OpenVentilator/OpenVentilator/hardware/Knob-4.sldprt

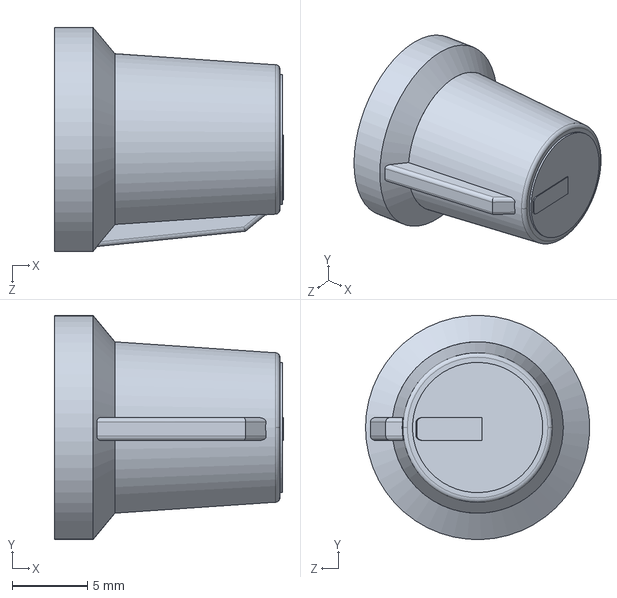
[picture p17: CAD file, 2020-04-01]
hardware/Knob-4.sldprt
15.2 x 14.9 x 14.9 mm
