OpenVentilator/OpenVentilator/hardware/PLEXI_DXF/lower_plate.DXF

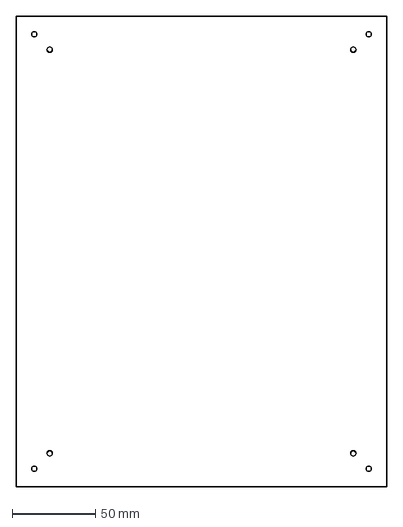
[picture p18: CAD file, 2020-03-31]
hardware/PLEXI_DXF/lower_plate.DXF
222.0 x 282.0 mm
