OpenVentilator/OpenVentilator/hardware/lower_gearbox_plate.SLDPRT

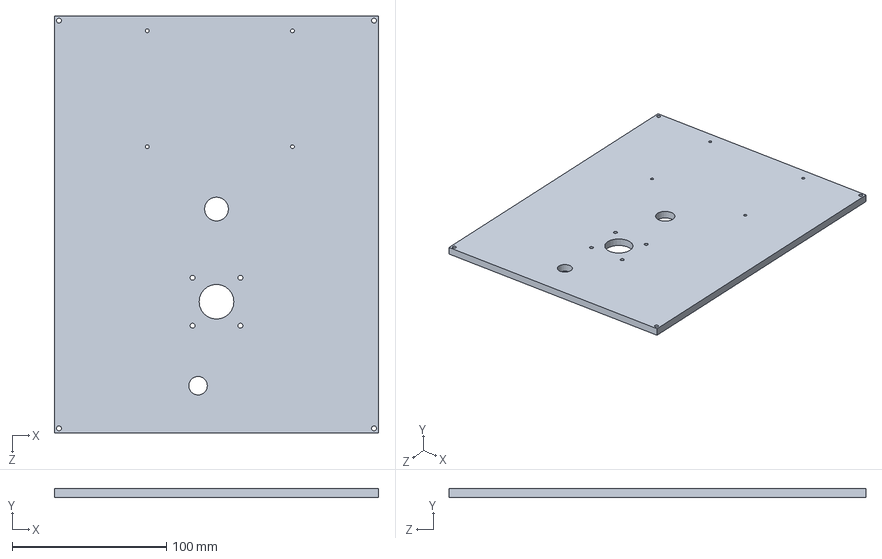
[picture p19: CAD file, 2020-04-01]
hardware/lower_gearbox_plate.SLDPRT
210.0 x 6.00 x 270.0 mm
