OpenVentilator/OpenVentilator/hardware/PLEXI_DXF/side_cover.DXF

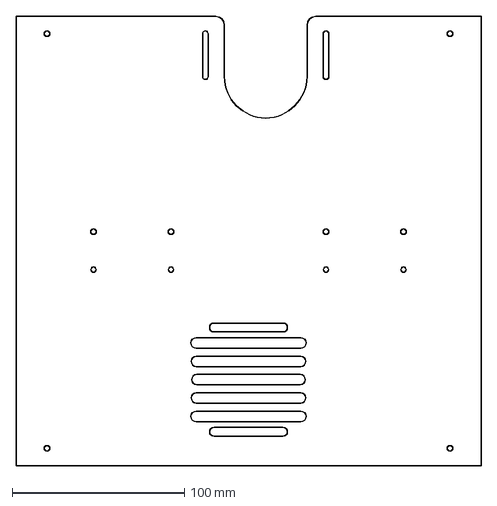
[picture p20: CAD file, 2020-03-31]
hardware/PLEXI_DXF/side_cover.DXF
270.0 x 260.8 mm
