OpenVentilator/OpenVentilator/hardware/lower_plate.SLDPRT

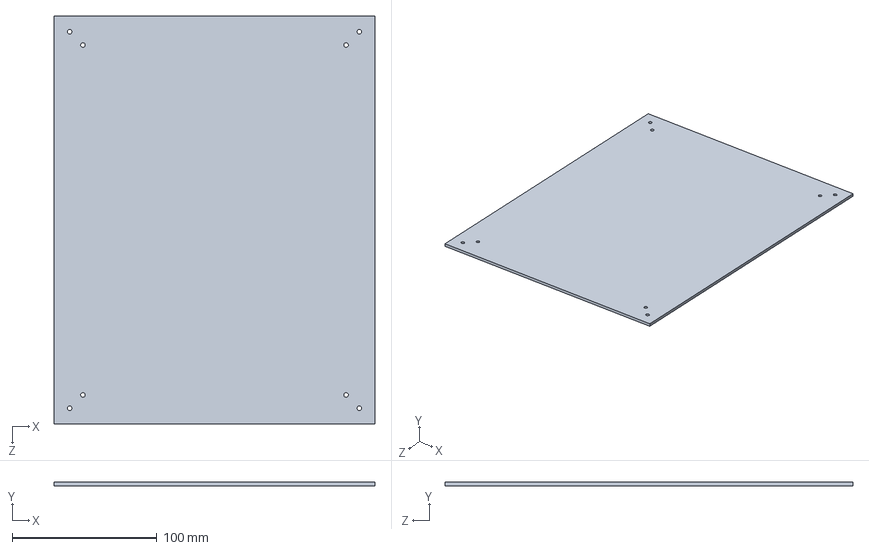
[picture p21: CAD file, 2020-03-31]
hardware/lower_plate.SLDPRT
222.0 x 2.50 x 282.0 mm
