OpenVentilator/OpenVentilator/hardware/PLEXI_DXF/spacershort.DXF

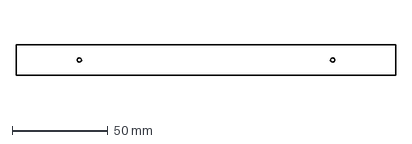
[picture p22: CAD file, 2020-03-31]
hardware/PLEXI_DXF/spacershort.DXF
198.0 x 16.0 mm
