OpenVentilator/OpenVentilator/hardware/PLEXI_DXF/motor_holder.DXF

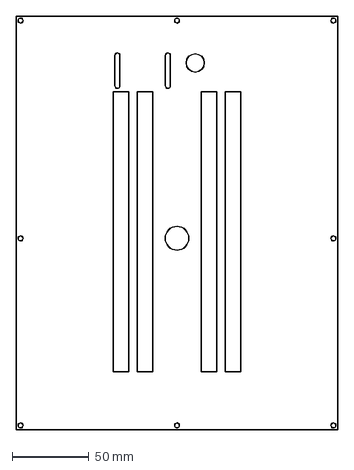
[picture p23: CAD file, 2020-03-31]
hardware/PLEXI_DXF/motor_holder.DXF
210.0 x 270.0 mm
