OpenVentilator/OpenVentilator/hardware/holder_zabalota.SLDPRT

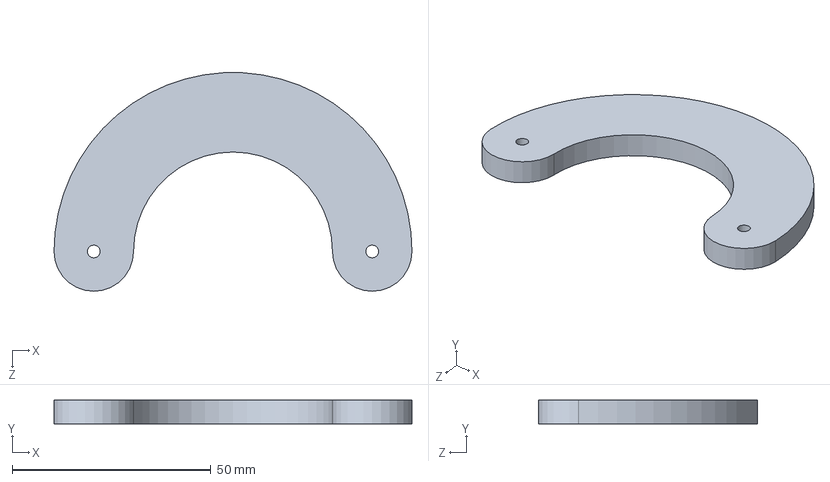
[picture p24: CAD file, 2020-03-31]
hardware/holder_zabalota.SLDPRT
90.0 x 6.00 x 54.9 mm
