OpenVentilator/OpenVentilator/hardware/PLEXI_DXF/side_cover_2.DXF

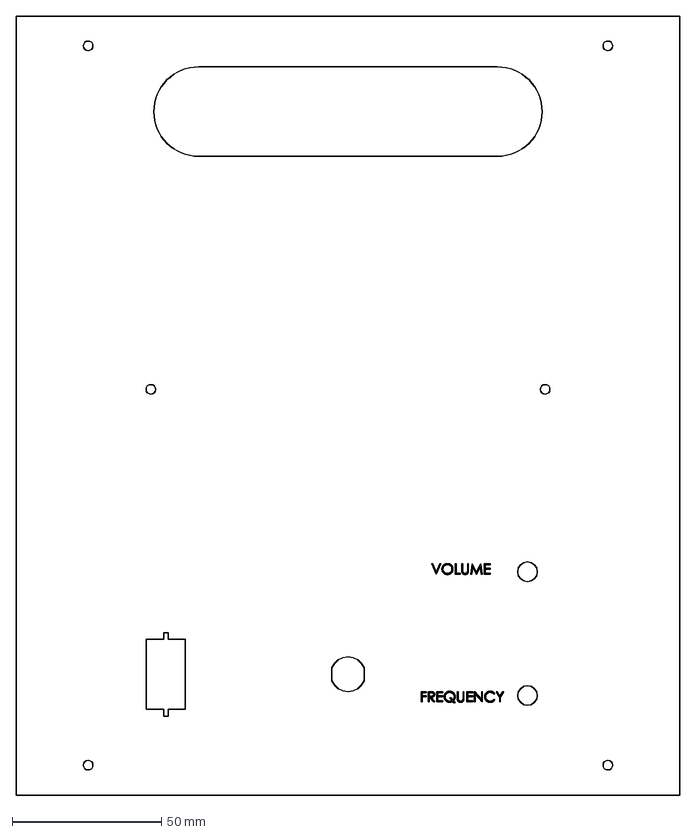
[picture p25: CAD file, 2020-03-31]
hardware/PLEXI_DXF/side_cover_2.DXF
222.0 x 260.8 mm
