OpenVentilator/OpenVentilator/hardware/ambu_adaptor_part2.SLDPRT

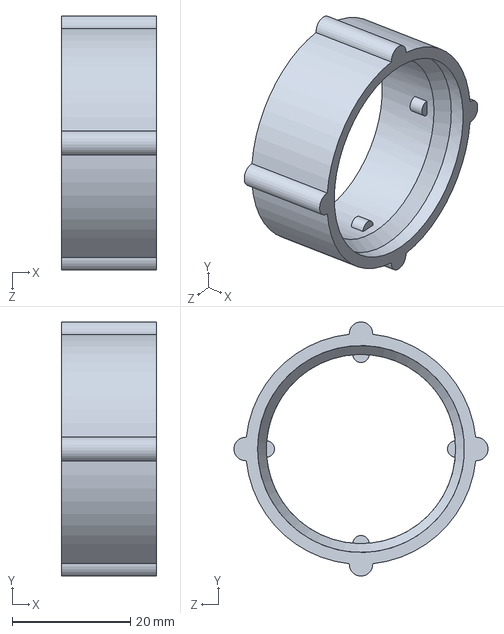
[picture p26: CAD file, 2020-03-31]
hardware/ambu_adaptor_part2.SLDPRT
16.0 x 43.0 x 43.0 mm
