OpenVentilator/OpenVentilator/hardware/PLEXI_DXF/spacerlong.DXF

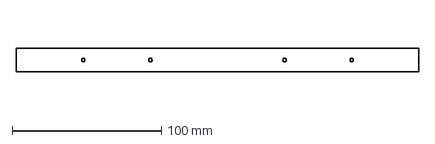
[picture p27: CAD file, 2020-03-31]
hardware/PLEXI_DXF/spacerlong.DXF
270.0 x 16.0 mm
