OpenVentilator/OpenVentilator/hardware/PLEXI_DXF/roulement_guides.DXF

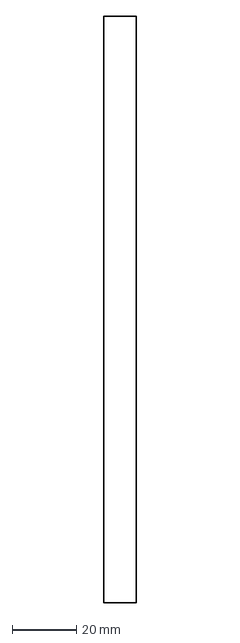
[picture p28: CAD file, 2020-03-31]
hardware/PLEXI_DXF/roulement_guides.DXF
10.0 x 182.6 mm
