OpenVentilator/OpenVentilator/hardware/spacershort.SLDPRT

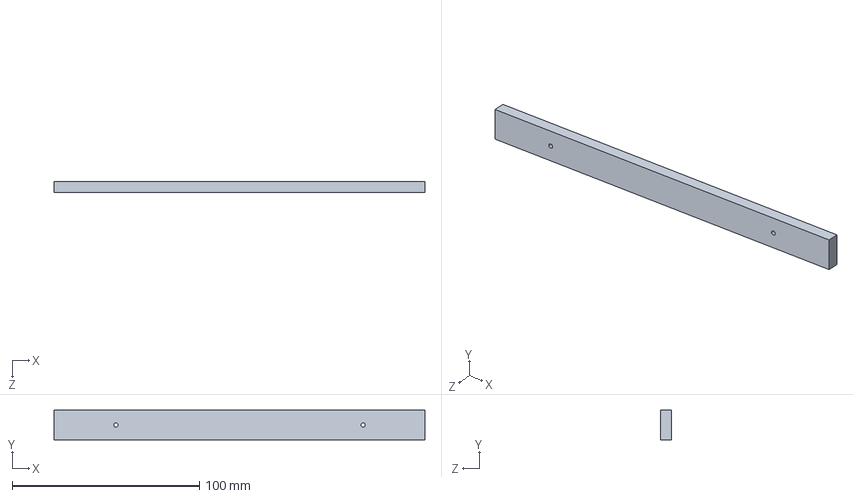
[picture p29: CAD file, 2020-03-31]
hardware/spacershort.SLDPRT
198.0 x 16.0 x 6.00 mm
