OpenVentilator/OpenVentilator/hardware/PLEXI_DXF/side_cover_big.DXF

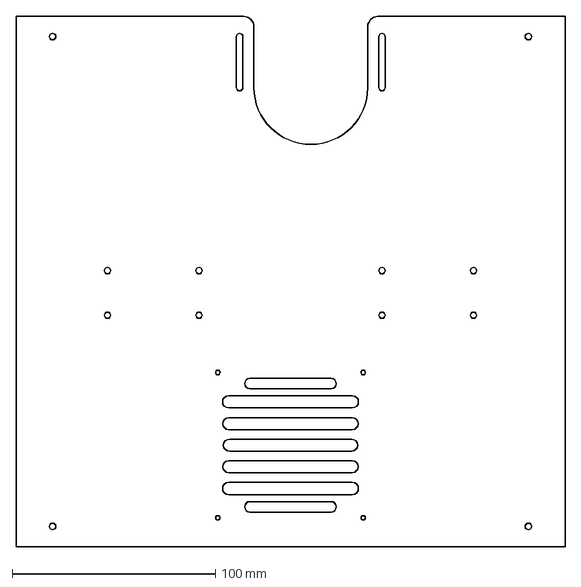
[picture p30: CAD file, 2020-03-31]
hardware/PLEXI_DXF/side_cover_big.DXF
270.0 x 260.8 mm
