OpenVentilator/OpenVentilator/hardware/PLEXI_DXF/top_chassis_plate.DXF

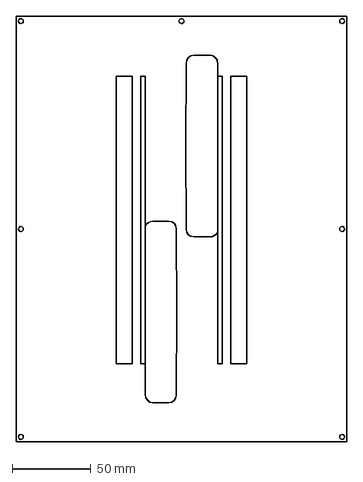
[picture p31: CAD file, 2020-03-31]
hardware/PLEXI_DXF/top_chassis_plate.DXF
210.0 x 270.0 mm
