OpenVentilator/OpenVentilator/hardware/side_cover.SLDPRT

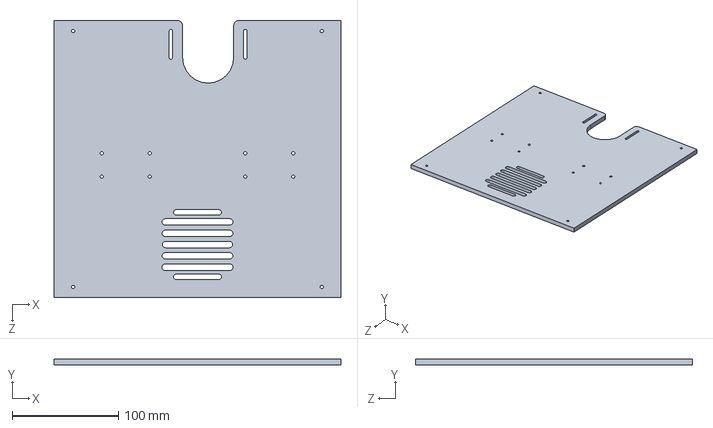
[picture p32: CAD file, 2020-03-31]
hardware/side_cover.SLDPRT
270.0 x 6.00 x 260.8 mm
