OpenVentilator/OpenVentilator/hardware/nema_17_47_gearbox_13.SLDPRT

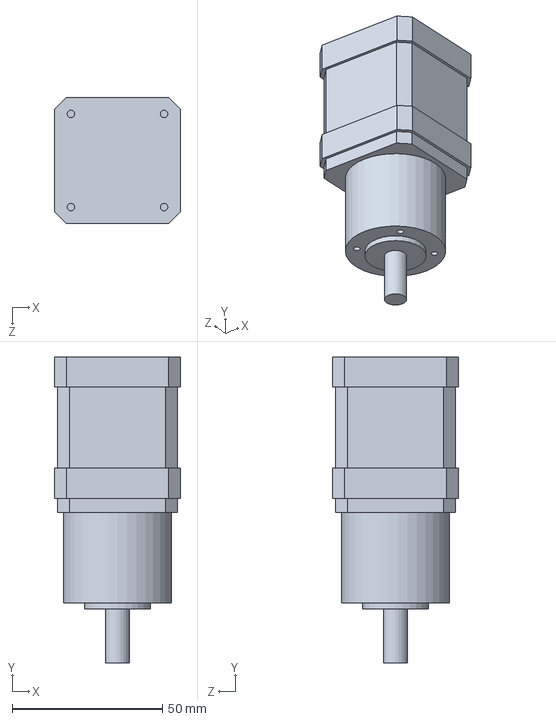
[picture p33: CAD file, 2020-03-31]
hardware/nema_17_47_gearbox_13.SLDPRT
42.0 x 101.8 x 42.0 mm
