OpenVentilator/OpenVentilator/hardware/AMBU_BAG.SLDPRT

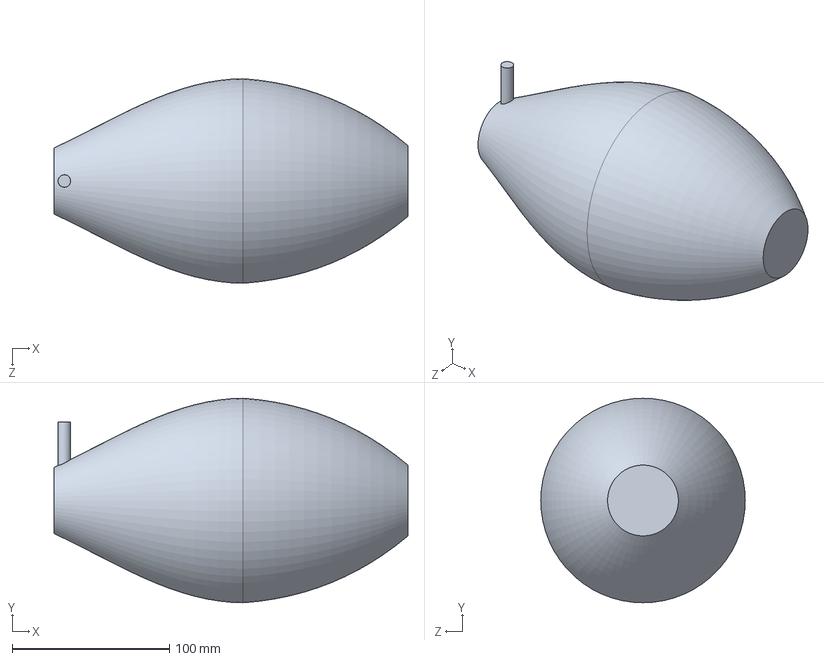
[picture p34: CAD file, 2020-03-31]
hardware/AMBU_BAG.SLDPRT
225.0 x 130.0 x 130.0 mm
