OpenVentilator/OpenVentilator/hardware/pusher_holder.SLDPRT

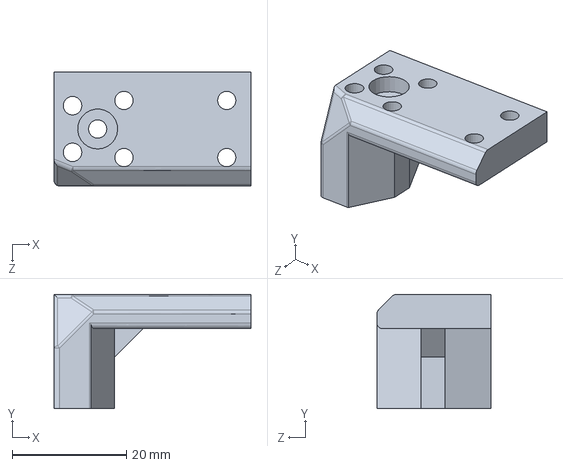
[picture p35: CAD file, 2020-03-31]
hardware/pusher_holder.SLDPRT
34.5 x 20.0 x 20.0 mm
