OpenVentilator/OpenVentilator/hardware/side_cover_2_bis.SLDPRT

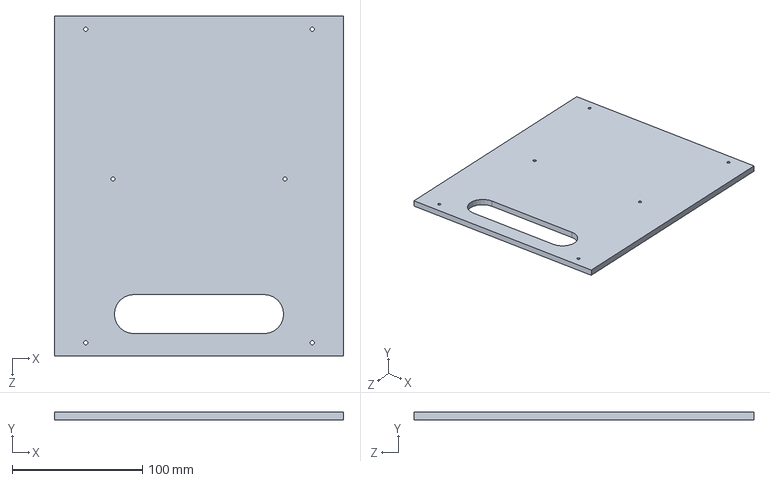
[picture p36: CAD file, 2020-03-31]
hardware/side_cover_2_bis.SLDPRT
222.0 x 6.00 x 260.8 mm
