OpenVentilator/OpenVentilator/hardware/spacerlong.SLDPRT

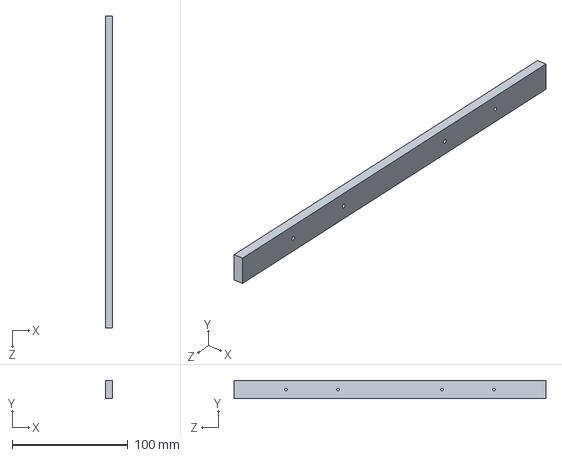
[picture p37: CAD file, 2020-03-31]
hardware/spacerlong.SLDPRT
6.00 x 16.0 x 270.0 mm
