OpenVentilator/OpenVentilator/hardware/pusher.SLDPRT

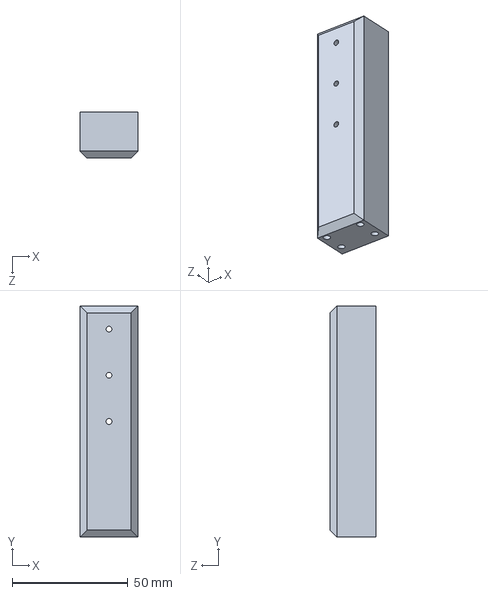
[picture p38: CAD file, 2020-03-31]
hardware/pusher.SLDPRT
25.0 x 100.0 x 20.0 mm
