OpenVentilator/OpenVentilator/hardware/spur_gear_copu.SLDPRT

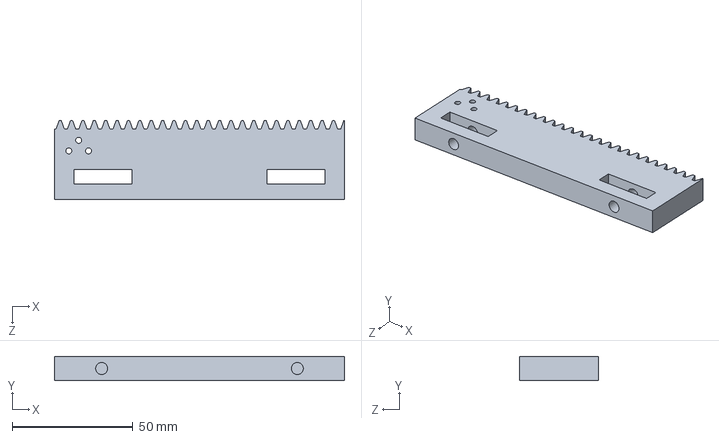
[picture p39: CAD file, 2020-03-31]
hardware/spur_gear_copu.SLDPRT
120.0 x 10.0 x 32.5 mm
