OpenVentilator/OpenVentilator/hardware/pusher_accee.SLDPRT

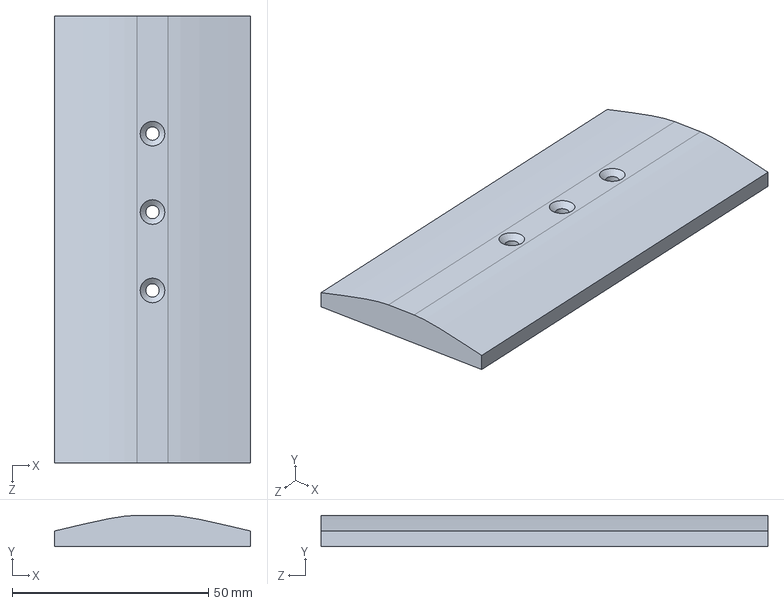
[picture p40: CAD file, 2020-03-31]
hardware/pusher_accee.SLDPRT
50.0 x 8.00 x 114.0 mm
