OpenVentilator/OpenVentilator/hardware/KD1208PTS3.step

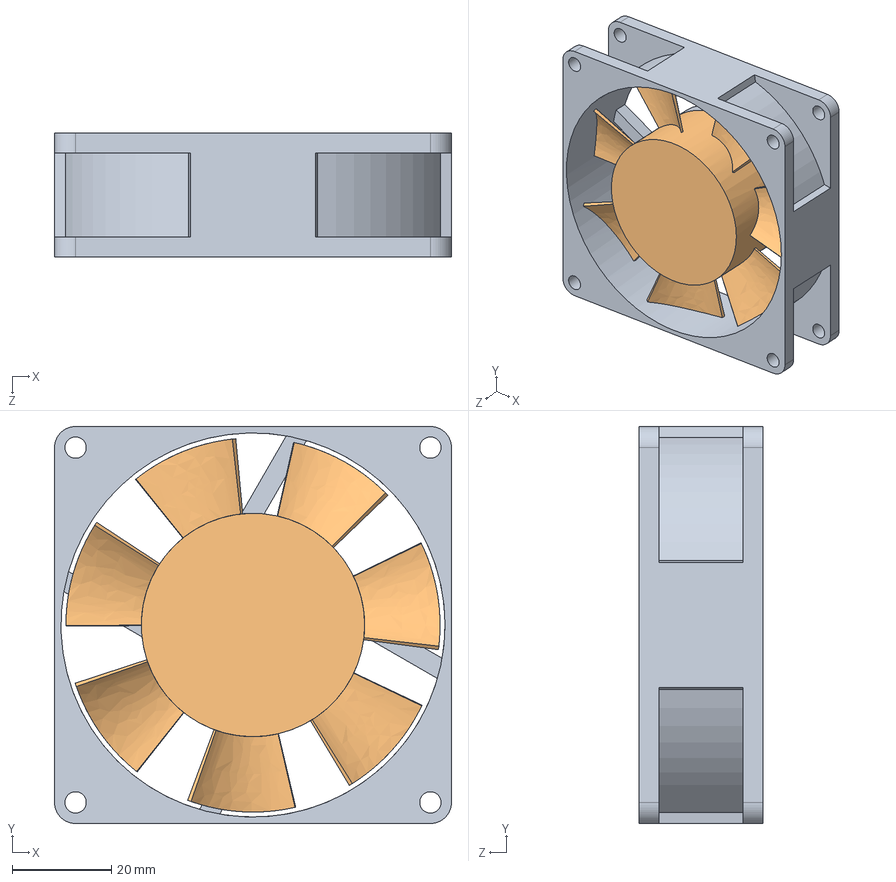
[picture p41: CAD file, 2020-03-31]
hardware/KD1208PTS3.step
80.0 x 80.0 x 25.0 mm
Fan_HouseKD1208PTS3_KD1208PTS3
FanKD1208PTS3_KD1208PTS3
