OpenVentilator/OpenVentilator/hardware/T_to_PEEP_adaptor.SLDPRT

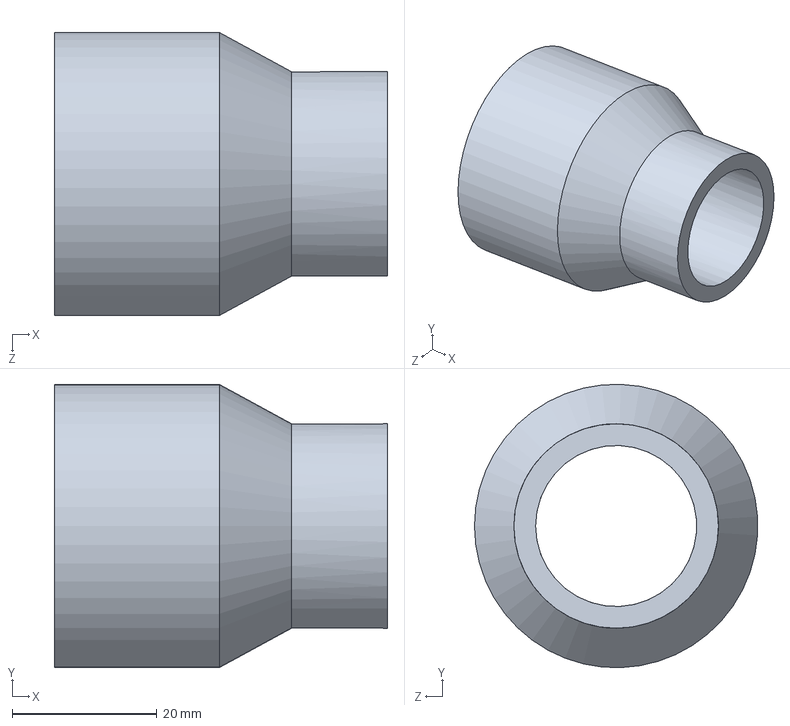
[picture p42: CAD file, 2020-03-31]
hardware/T_to_PEEP_adaptor.SLDPRT
46.0 x 39.1 x 39.1 mm
