OpenVentilator/OpenVentilator/hardware/ambu_adaptor_part1.SLDPRT

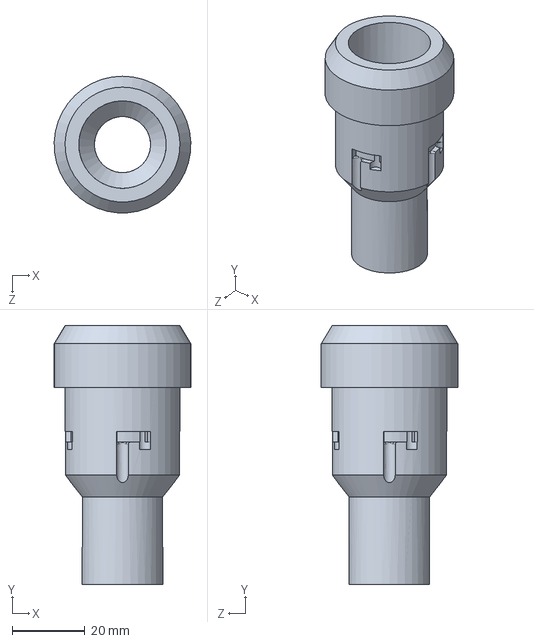
[picture p43: CAD file, 2020-03-31]
hardware/ambu_adaptor_part1.SLDPRT
37.5 x 71.0 x 37.4 mm
