OpenVentilator/OpenVentilator/hardware/top_chassis_plate.SLDPRT

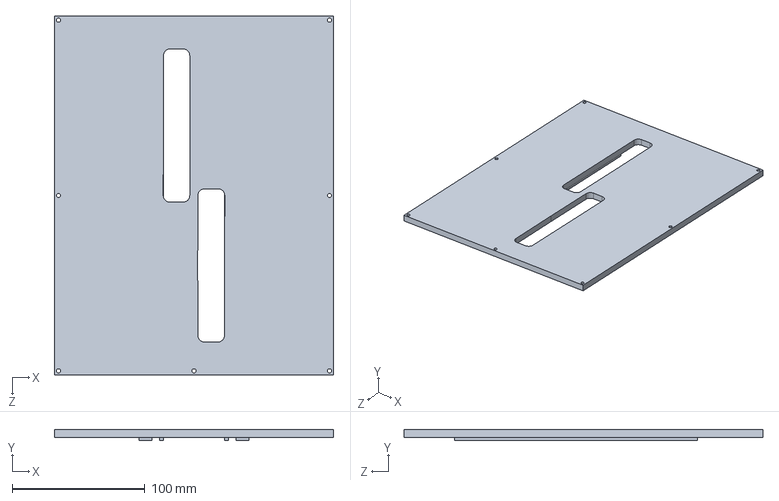
[picture p44: CAD file, 2020-03-31]
hardware/top_chassis_plate.SLDPRT
210.0 x 8.00 x 270.0 mm
