OpenVentilator/OpenVentilator/hardware/peep_to_tube_adapter.SLDPRT

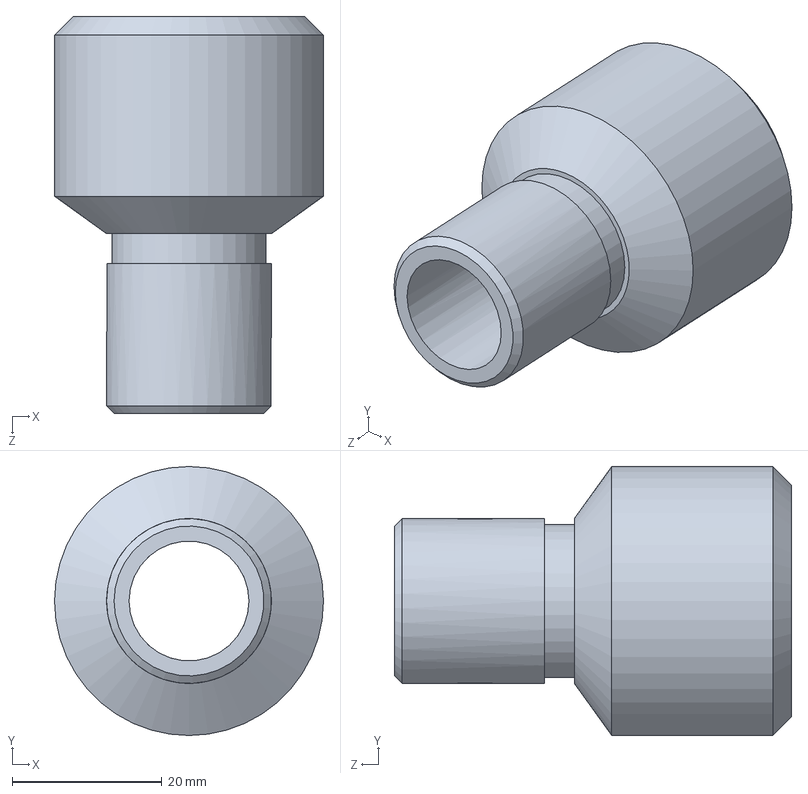
[picture p45: CAD file, 2020-03-31]
hardware/peep_to_tube_adapter.SLDPRT
35.9 x 35.9 x 53.0 mm
