OpenVentilator/OpenVentilator/hardware/tactile_switch_smd.SLDPRT

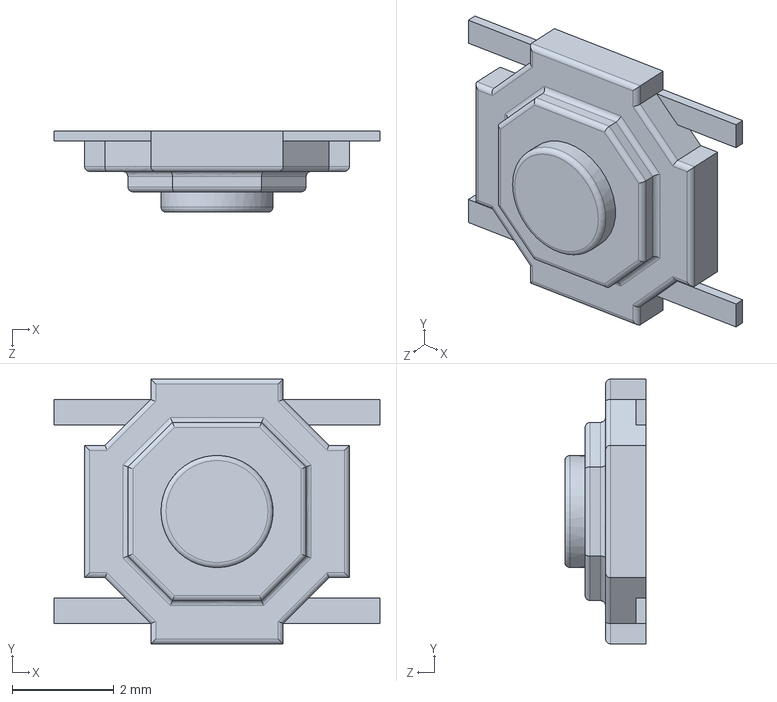
[picture p46: CAD file, 2020-03-25]
hardware/tactile_switch_smd.SLDPRT
6.40 x 5.20 x 1.60 mm
