OpenVentilator/OpenVentilator/hardware/bracket.SLDPRT

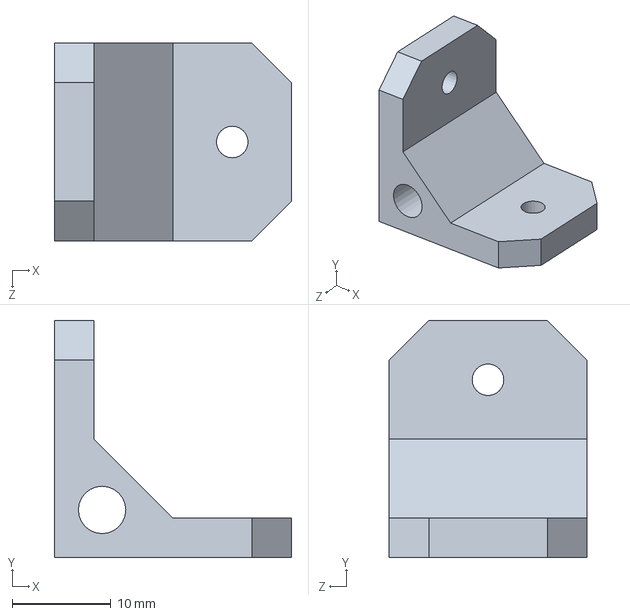
[picture p47: CAD file, 2020-03-25]
hardware/bracket.SLDPRT
24.0 x 24.0 x 20.0 mm
