OpenVentilator/OpenVentilator/hardware/Motor Driver.SLDPRT

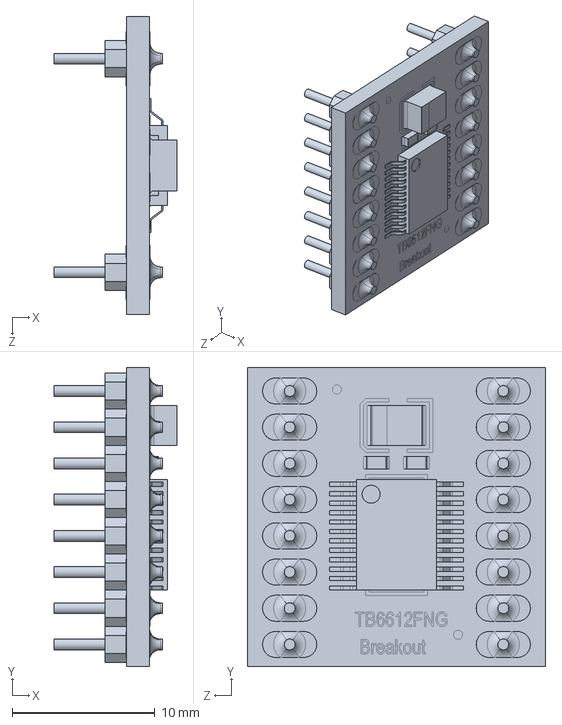
[picture p48: CAD file, 2020-03-25]
hardware/Motor Driver.SLDPRT
8.62 x 21.0 x 20.9 mm
