OpenVentilator/OpenVentilator/hardware/spacer15mm.SLDPRT

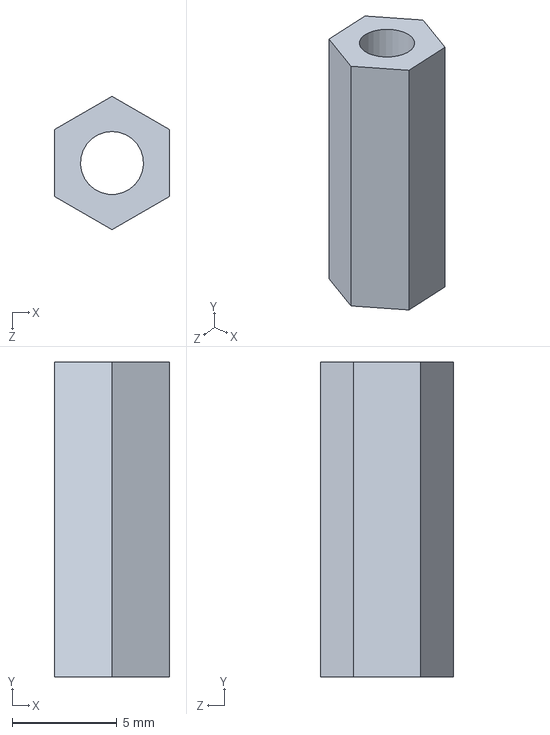
[picture p49: CAD file, 2020-03-25]
hardware/spacer15mm.SLDPRT
5.50 x 15.0 x 6.35 mm
