OpenVentilator/OpenVentilator/hardware/connector_2_pins.SLDPRT

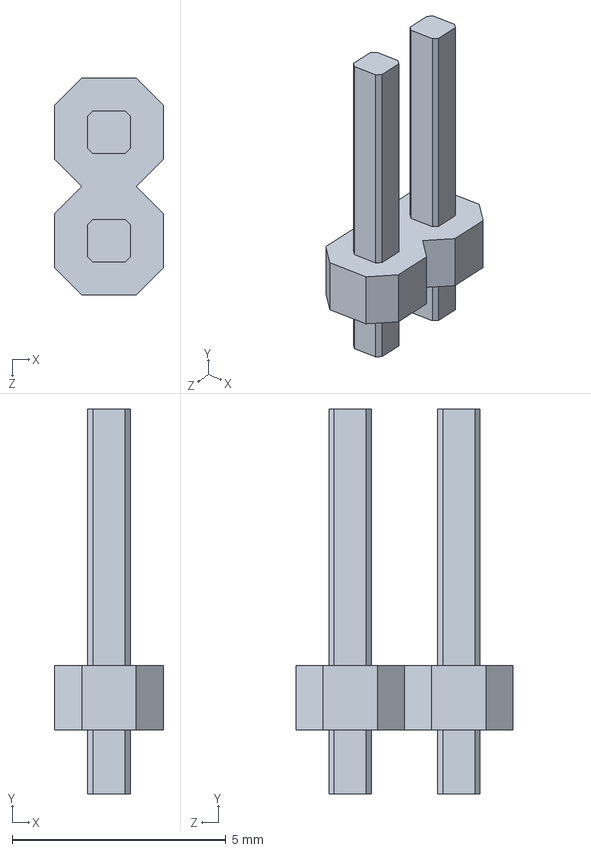
[picture p50: CAD file, 2020-03-25]
hardware/connector_2_pins.SLDPRT
2.54 x 9.00 x 5.08 mm
