OpenVentilator/OpenVentilator/hardware/7805.SLDPRT

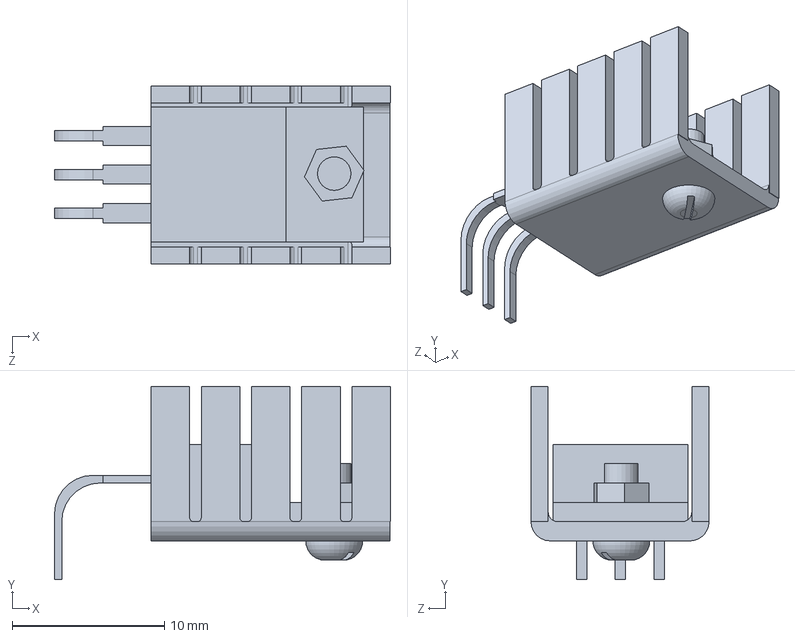
[picture p51: CAD file, 2020-03-25]
hardware/7805.SLDPRT
22.1 x 12.7 x 11.7 mm
