OpenVentilator/OpenVentilator/hardware/Tapa.SLDPRT

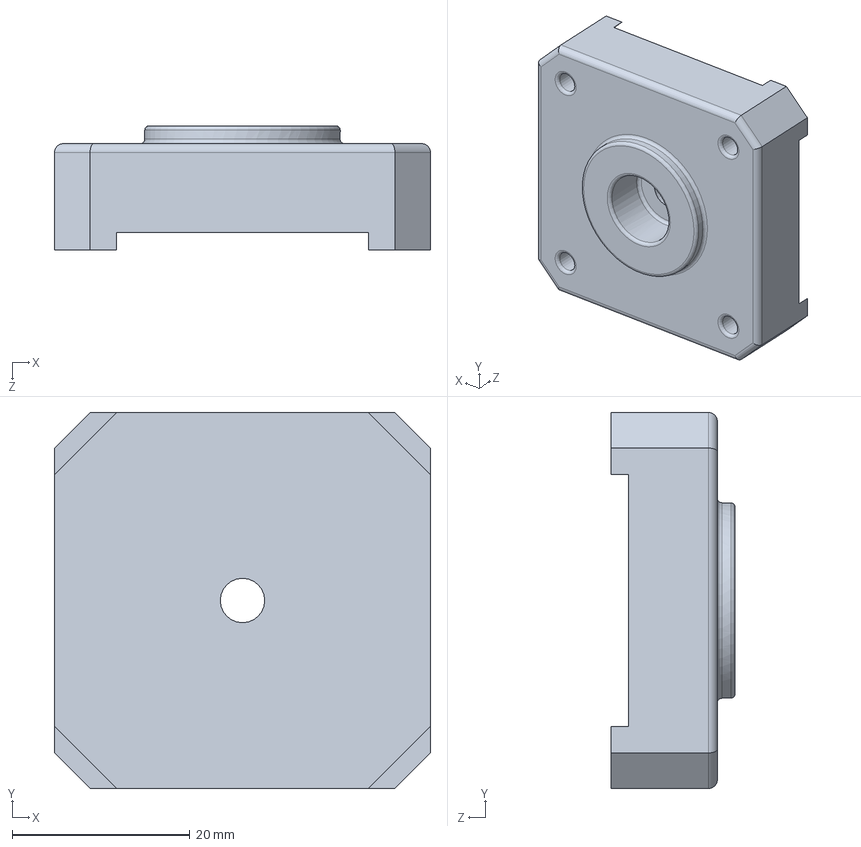
[picture p52: CAD file, 2020-03-25]
hardware/Tapa.SLDPRT
42.3 x 42.3 x 14.0 mm
