OpenVentilator/OpenVentilator/hardware/connector_3_pins.SLDPRT

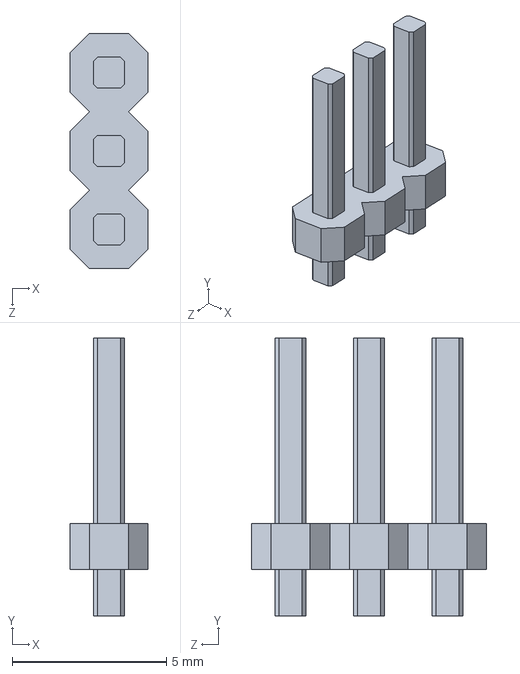
[picture p53: CAD file, 2020-03-25]
hardware/connector_3_pins.SLDPRT
2.54 x 9.00 x 7.62 mm
