OpenVentilator/OpenVentilator/hardware/roulement_guides.SLDPRT

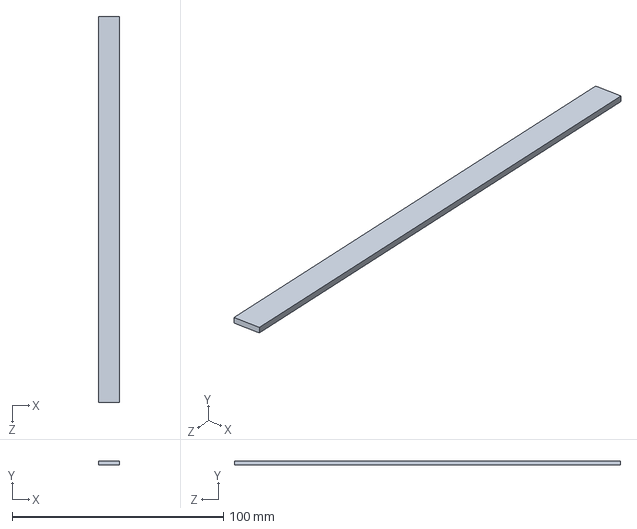
[picture p54: CAD file, 2020-03-25]
hardware/roulement_guides.SLDPRT
10.0 x 2.00 x 182.6 mm
