OpenVentilator/OpenVentilator/hardware/resonator16mhz.SLDPRT

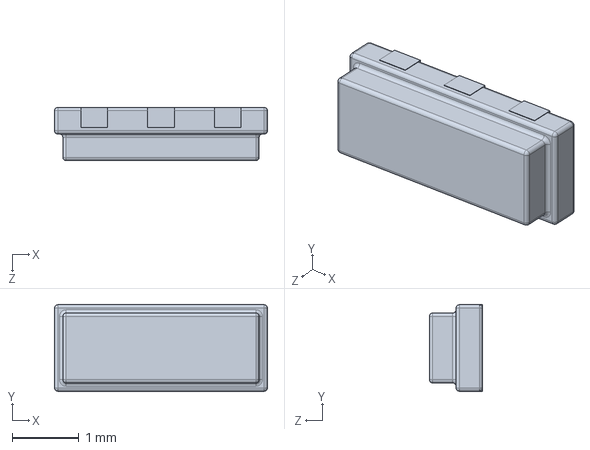
[picture p55: CAD file, 2020-03-25]
hardware/resonator16mhz.SLDPRT
3.20 x 1.31 x 0.801 mm
