OpenVentilator/OpenVentilator/hardware/connector_8_pins.SLDPRT

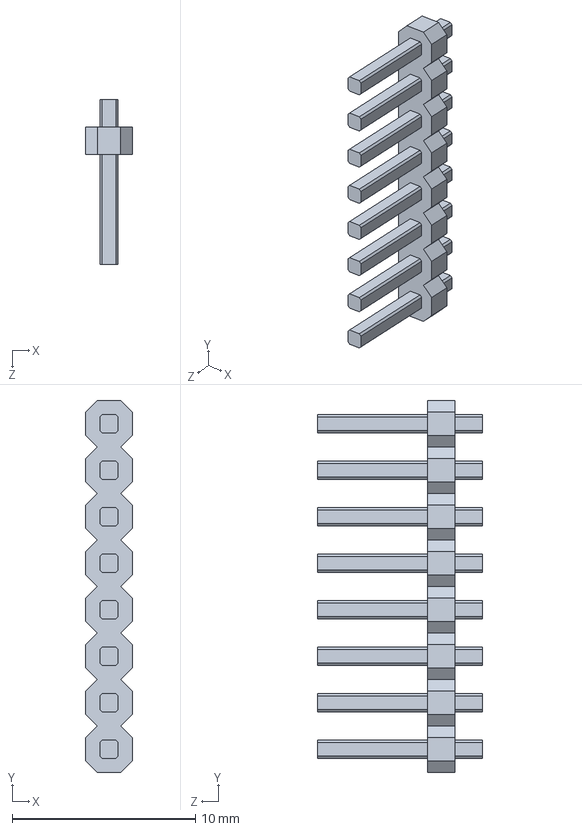
[picture p56: CAD file, 2020-03-25]
hardware/connector_8_pins.SLDPRT
2.54 x 20.3 x 9.00 mm
