OpenVentilator/OpenVentilator/hardware/pcb.SLDPRT

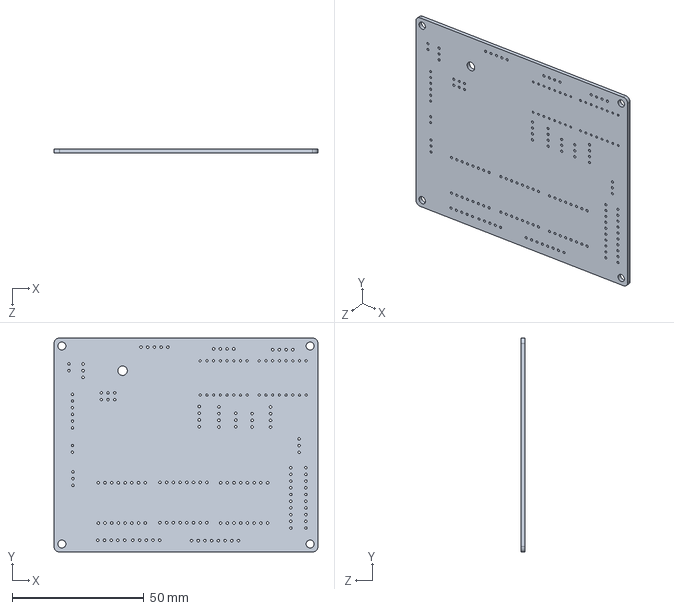
[picture p57: CAD file, 2020-03-25]
hardware/pcb.SLDPRT
100.0 x 81.0 x 1.50 mm
