OpenVentilator/OpenVentilator/hardware/limit_switch.SLDPRT

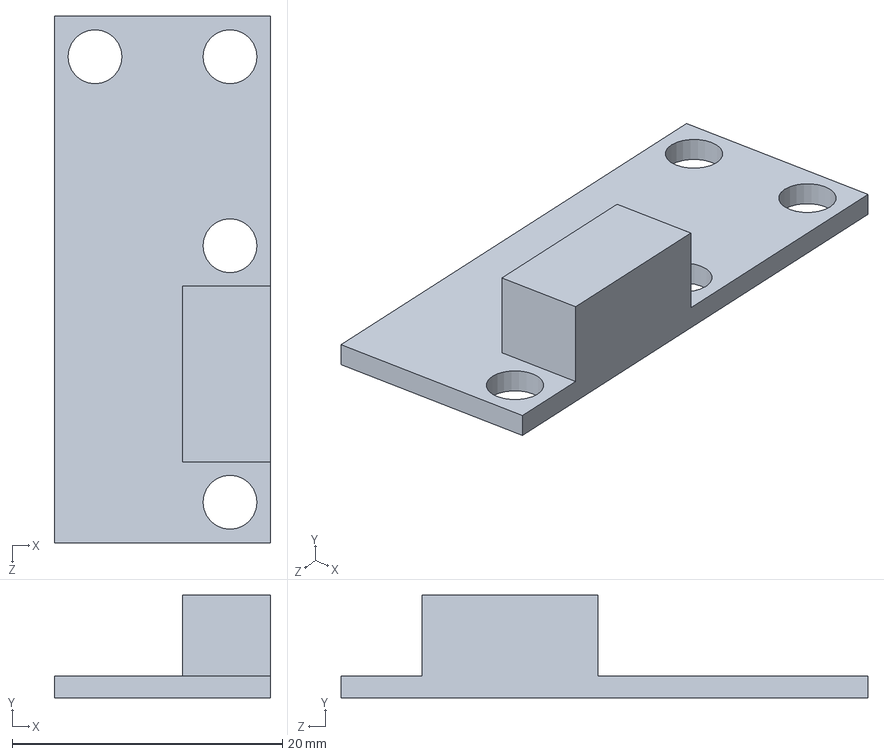
[picture p58: CAD file, 2020-03-25]
hardware/limit_switch.SLDPRT
16.0 x 7.60 x 39.0 mm
