OpenVentilator/OpenVentilator/hardware/connector_4_pins.SLDPRT

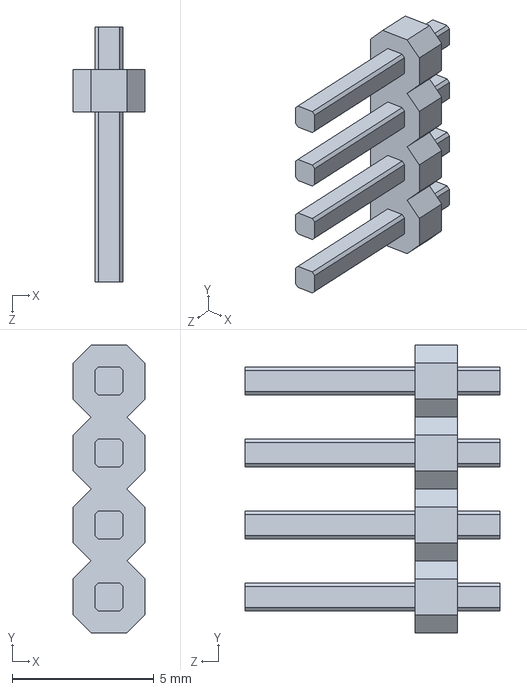
[picture p59: CAD file, 2020-03-25]
hardware/connector_4_pins.SLDPRT
2.54 x 10.2 x 9.00 mm
