OpenVentilator/OpenVentilator/hardware/rubber_supports.SLDPRT

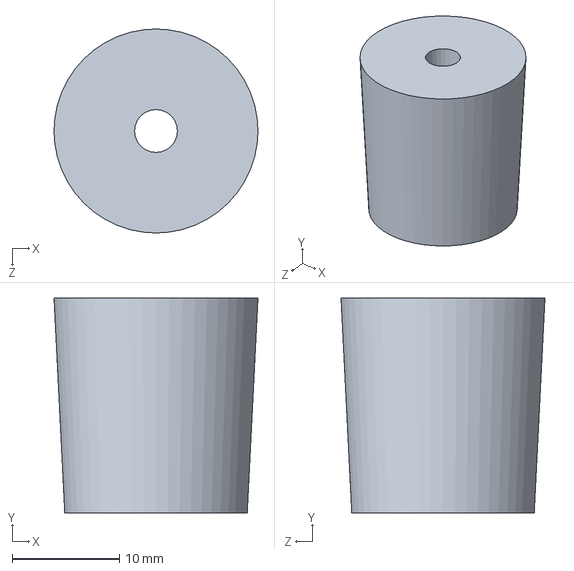
[picture p60: CAD file, 2020-03-25]
hardware/rubber_supports.SLDPRT
19.0 x 20.0 x 19.0 mm
