OpenVentilator/OpenVentilator/hardware/connector_6_pins.SLDPRT

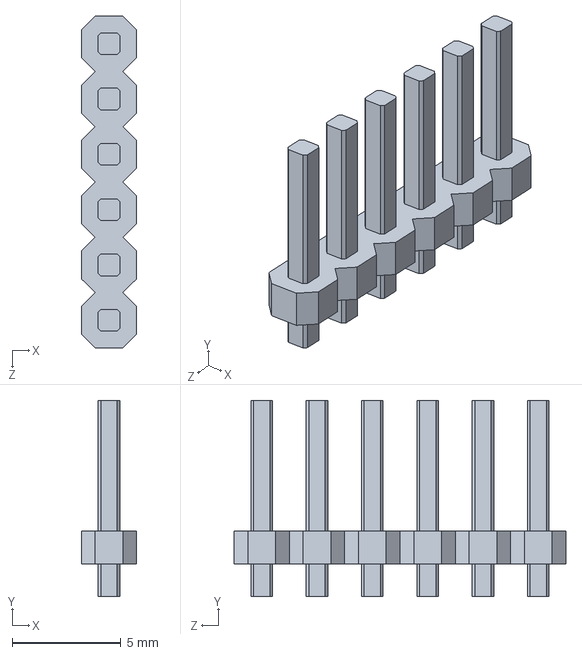
[picture p61: CAD file, 2020-03-25]
hardware/connector_6_pins.SLDPRT
2.54 x 9.00 x 15.2 mm
