OpenVentilator/OpenVentilator/hardware/mks-tb6600.SLDPRT

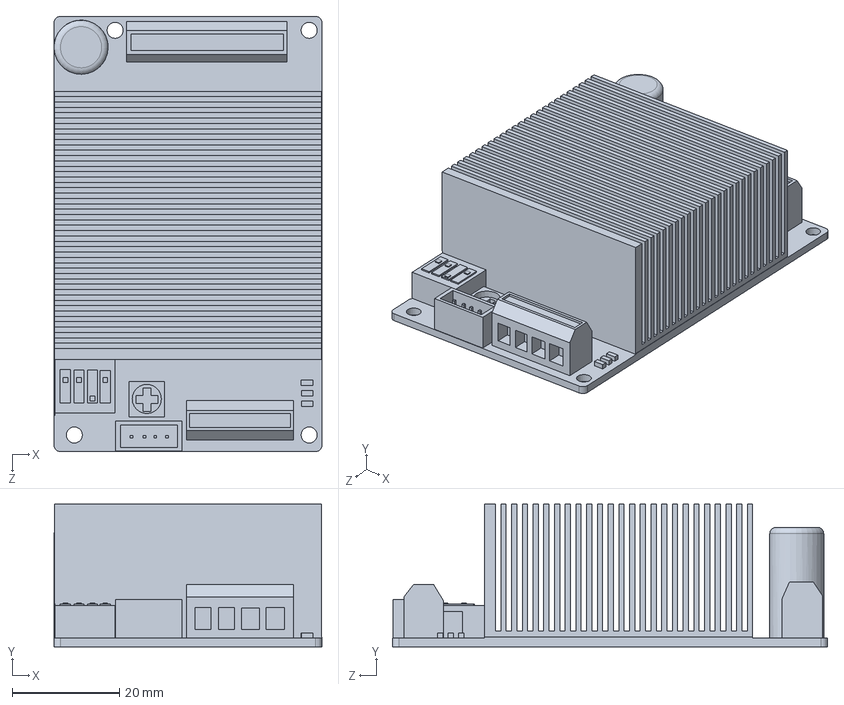
[picture p62: CAD file, 2020-03-25]
hardware/mks-tb6600.SLDPRT
50.0 x 26.6 x 81.2 mm
