OpenVentilator/OpenVentilator/hardware/Base.SLDPRT

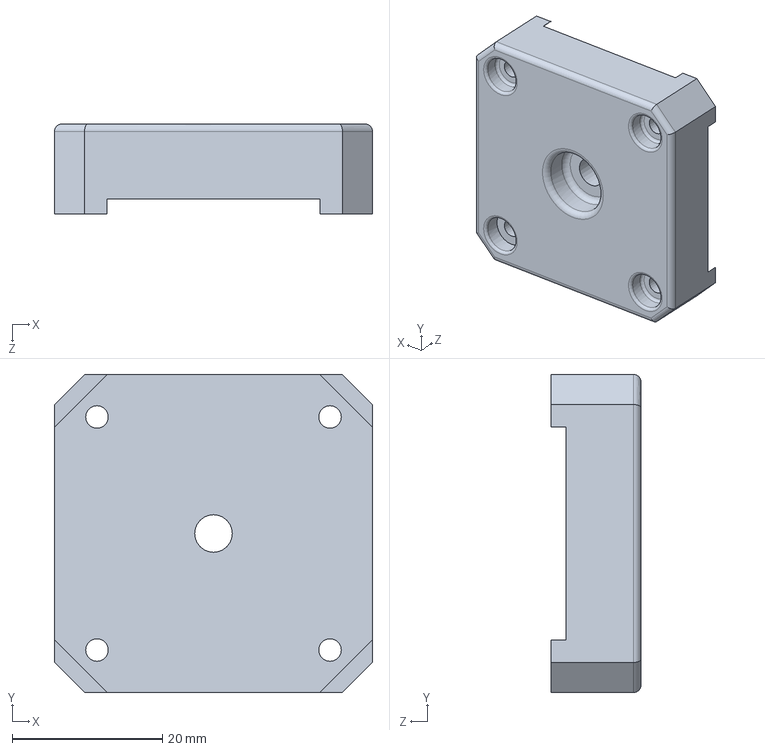
[picture p63: CAD file, 2020-03-25]
hardware/Base.SLDPRT
42.3 x 42.3 x 12.0 mm
