OpenVentilator/OpenVentilator/hardware/Cuerpo.SLDPRT

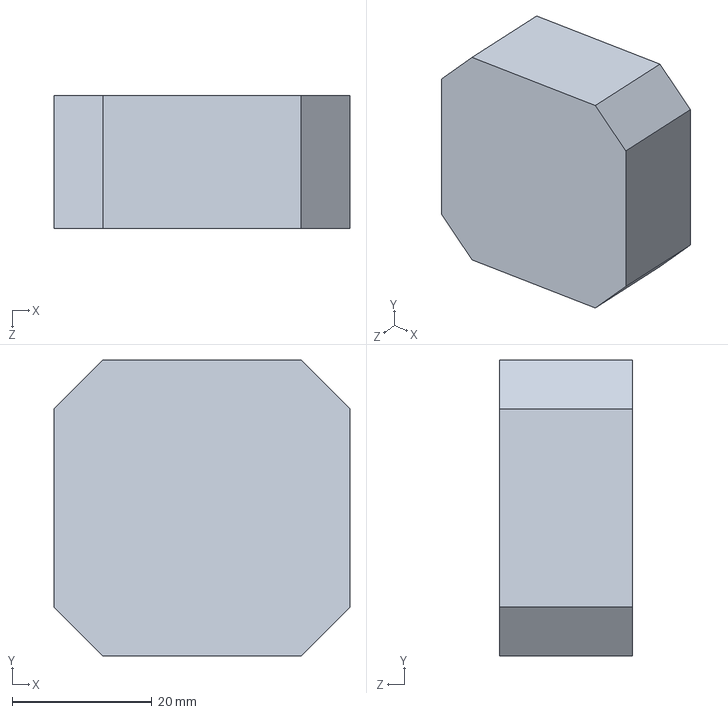
[picture p64: CAD file, 2020-03-25]
hardware/Cuerpo.SLDPRT
42.3 x 42.3 x 19.0 mm
