OpenVentilator/OpenVentilator/hardware/atmega2560.SLDPRT

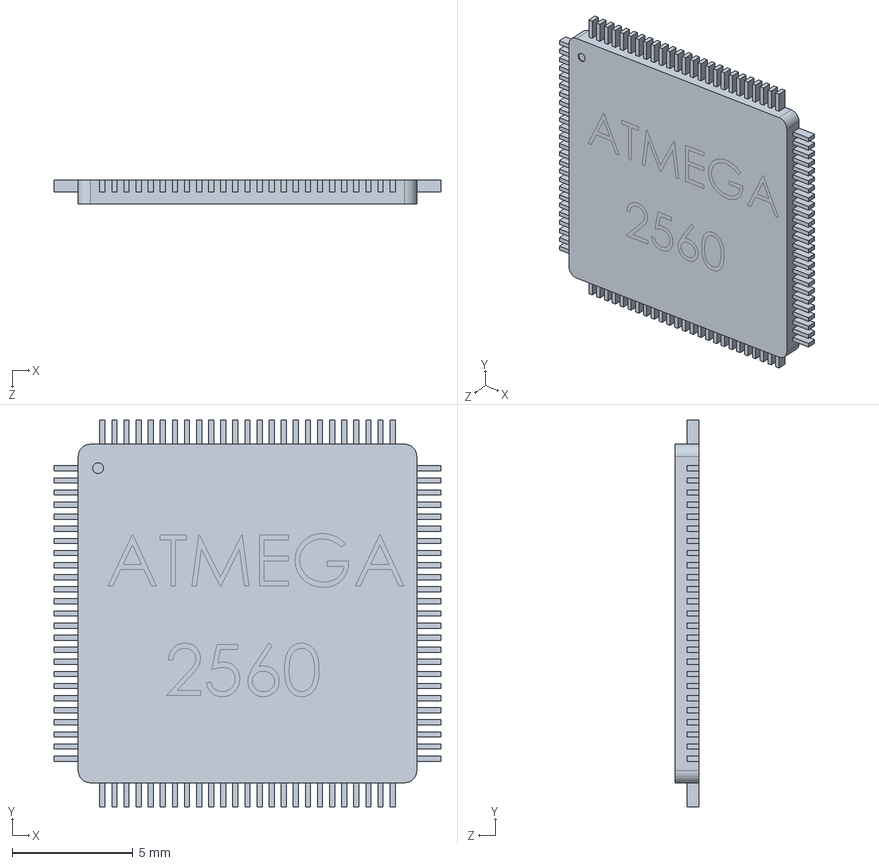
[picture p65: CAD file, 2020-03-25]
hardware/atmega2560.SLDPRT
16.0 x 16.0 x 1.00 mm
