OpenVentilator/OpenVentilator/hardware/connector_5_pins.SLDPRT

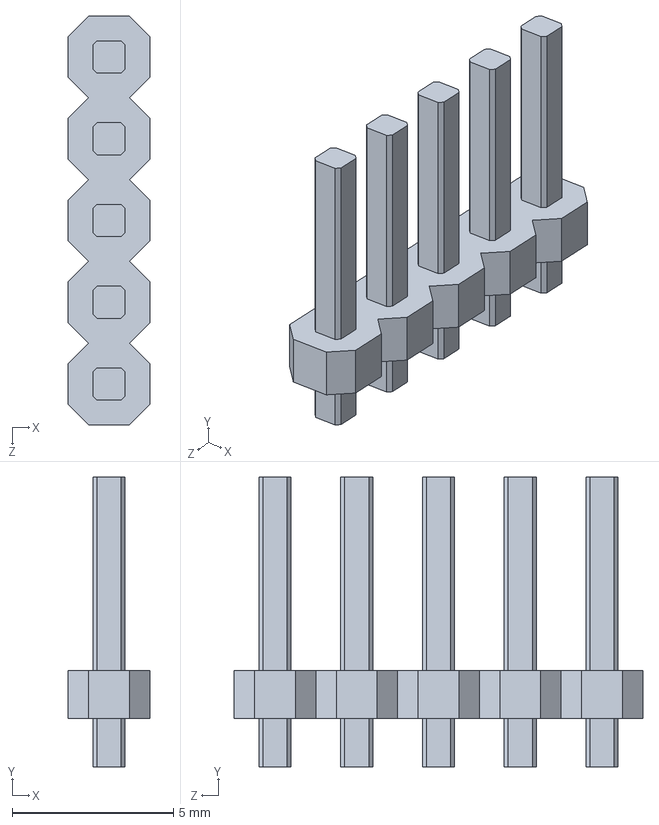
[picture p66: CAD file, 2020-03-25]
hardware/connector_5_pins.SLDPRT
2.54 x 9.00 x 12.7 mm
