OpenVentilator/OpenVentilator/hardware/Eje.SLDPRT

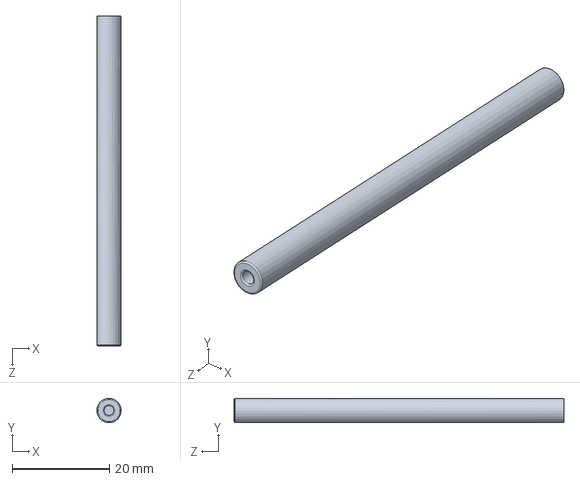
[picture p67: CAD file, 2020-03-25]
hardware/Eje.SLDPRT
5.00 x 5.00 x 68.0 mm
